kodyvajjha/zymoscope/firmware/main/display/oled.c

/*
 * SSD1306 128x64 OLED I2C driver with built-in 8x8 font
 *
 * Assumes the I2C master driver is already installed (by bme280_init).
 * Shares I2C port 0 with the BME280.
 */

#include "oled.h"

#include <math.h>
#include <string.h>
#include <stdio.h>
#include "driver/i2c.h"
#include "esp_log.h"
#include "sensor/bme280_i2c.h"   /* for BME280_I2C_PORT */

static const char *TAG = "oled";

/* Framebuffer: 128 x 64 pixels = 128 x 8 pages of 8 vertical bits */
#define FB_SIZE  (OLED_WIDTH * (OLED_HEIGHT / 8))
static uint8_t fb[FB_SIZE];

/* ------------------------------------------------------------------ */
/*  Built-in 8x8 ASCII font (printable range 0x20..0x7E)             */
/* ------------------------------------------------------------------ */
static const uint8_t font8x8[][8] = {
    /* 0x20 ' ' */ {0x00,0x00,0x00,0x00,0x00,0x00,0x00,0x00},
    /* 0x21 '!' */ {0x00,0x00,0x06,0x5F,0x5F,0x06,0x00,0x00},
    /* 0x22 '"' */ {0x00,0x03,0x07,0x00,0x00,0x07,0x03,0x00},
    /* 0x23 '#' */ {0x14,0x7F,0x7F,0x14,0x7F,0x7F,0x14,0x00},
    /* 0x24 '$' */ {0x24,0x2E,0x6B,0x6B,0x3A,0x12,0x00,0x00},
    /* 0x25 '%' */ {0x46,0x66,0x30,0x18,0x0C,0x66,0x62,0x00},
    /* 0x26 '&' */ {0x30,0x7A,0x4F,0x5D,0x37,0x7A,0x48,0x00},
    /* 0x27 '\''*/ {0x00,0x04,0x07,0x03,0x00,0x00,0x00,0x00},
    /* 0x28 '(' */ {0x00,0x1C,0x3E,0x63,0x41,0x00,0x00,0x00},
    /* 0x29 ')' */ {0x00,0x41,0x63,0x3E,0x1C,0x00,0x00,0x00},
    /* 0x2A '*' */ {0x08,0x2A,0x3E,0x1C,0x1C,0x3E,0x2A,0x08},
    /* 0x2B '+' */ {0x08,0x08,0x3E,0x3E,0x08,0x08,0x00,0x00},
    /* 0x2C ',' */ {0x00,0x80,0xE0,0x60,0x00,0x00,0x00,0x00},
    /* 0x2D '-' */ {0x08,0x08,0x08,0x08,0x08,0x08,0x00,0x00},
    /* 0x2E '.' */ {0x00,0x00,0x60,0x60,0x00,0x00,0x00,0x00},
    /* 0x2F '/' */ {0x60,0x30,0x18,0x0C,0x06,0x03,0x01,0x00},
    /* 0x30 '0' */ {0x3E,0x7F,0x71,0x59,0x4D,0x7F,0x3E,0x00},
    /* 0x31 '1' */ {0x40,0x42,0x7F,0x7F,0x40,0x40,0x00,0x00},
    /* 0x32 '2' */ {0x62,0x73,0x59,0x49,0x6F,0x66,0x00,0x00},
    /* 0x33 '3' */ {0x22,0x63,0x49,0x49,0x7F,0x36,0x00,0x00},
    /* 0x34 '4' */ {0x18,0x1C,0x16,0x53,0x7F,0x7F,0x50,0x00},
    /* 0x35 '5' */ {0x27,0x67,0x45,0x45,0x7D,0x39,0x00,0x00},
    /* 0x36 '6' */ {0x3C,0x7E,0x4B,0x49,0x79,0x30,0x00,0x00},
    /* 0x37 '7' */ {0x03,0x03,0x71,0x79,0x0F,0x07,0x00,0x00},
    /* 0x38 '8' */ {0x36,0x7F,0x49,0x49,0x7F,0x36,0x00,0x00},
    /* 0x39 '9' */ {0x06,0x4F,0x49,0x69,0x3F,0x1E,0x00,0x00},
    /* 0x3A ':' */ {0x00,0x00,0x36,0x36,0x00,0x00,0x00,0x00},
    /* 0x3B ';' */ {0x00,0x80,0xF6,0x76,0x00,0x00,0x00,0x00},
    /* 0x3C '<' */ {0x08,0x1C,0x36,0x63,0x41,0x00,0x00,0x00},
    /* 0x3D '=' */ {0x24,0x24,0x24,0x24,0x24,0x24,0x00,0x00},
    /* 0x3E '>' */ {0x00,0x41,0x63,0x36,0x1C,0x08,0x00,0x00},
    /* 0x3F '?' */ {0x02,0x03,0x51,0x59,0x0F,0x06,0x00,0x00},
    /* 0x40 '@' */ {0x3E,0x7F,0x41,0x5D,0x5D,0x1F,0x1E,0x00},
    /* 0x41 'A' */ {0x7C,0x7E,0x13,0x13,0x7E,0x7C,0x00,0x00},
    /* 0x42 'B' */ {0x41,0x7F,0x7F,0x49,0x49,0x7F,0x36,0x00},
    /* 0x43 'C' */ {0x1C,0x3E,0x63,0x41,0x41,0x63,0x22,0x00},
    /* 0x44 'D' */ {0x41,0x7F,0x7F,0x41,0x63,0x3E,0x1C,0x00},
    /* 0x45 'E' */ {0x41,0x7F,0x7F,0x49,0x5D,0x41,0x63,0x00},
    /* 0x46 'F' */ {0x41,0x7F,0x7F,0x49,0x1D,0x01,0x03,0x00},
    /* 0x47 'G' */ {0x1C,0x3E,0x63,0x41,0x51,0x73,0x72,0x00},
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
};

/* ------------------------------------------------------------------ */
/*  SSD1306 I2C helpers                                               */
/* ------------------------------------------------------------------ */

static esp_err_t oled_send_cmd(uint8_t cmd)
{
    uint8_t buf[2] = { 0x00, cmd };   /* Co=0, D/C#=0 (command) */
    return i2c_master_write_to_device(BME280_I2C_PORT, OLED_I2C_ADDR,
                                      buf, sizeof(buf),
                                      pdMS_TO_TICKS(100));
}

static esp_err_t oled_send_data(const uint8_t *data, size_t len)
{
    /* Build buffer: control byte (0x40 = Co=0, D/C#=1) + data */
    uint8_t *buf = malloc(len + 1);
    if (!buf) return ESP_ERR_NO_MEM;
    buf[0] = 0x40;
    memcpy(buf + 1, data, len);
    esp_err_t err = i2c_master_write_to_device(BME280_I2C_PORT, OLED_I2C_ADDR,
                                                buf, len + 1,
                                                pdMS_TO_TICKS(200));
    free(buf);
    return err;
}

/** Push the entire framebuffer to the display. */
static void oled_flush(void)
{
    /* Set column address 0..127 */
    oled_send_cmd(0x21); oled_send_cmd(0x00); oled_send_cmd(0x7F);
    /* Set page address 0..7 */
    oled_send_cmd(0x22); oled_send_cmd(0x00); oled_send_cmd(0x07);

    /* Send in 128-byte (one page) chunks to stay within I2C limits */
    for (int page = 0; page < 8; page++) {
        oled_send_data(&fb[page * OLED_WIDTH], OLED_WIDTH);
    }
}

/* ------------------------------------------------------------------ */
/*  Text rendering into the framebuffer                               */
/* ------------------------------------------------------------------ */

/**
 * Draw a character at pixel position (x, page).
 * page is 0..7 (each page = 8 vertical pixels).
 */
static void fb_putchar(int x, int page, char c)
{
    if (c < 0x20 || c > 0x7E) c = '?';
    int idx = c - 0x20;
    int offset = page * OLED_WIDTH + x;
    if (offset + 8 > FB_SIZE) return;
    memcpy(&fb[offset], font8x8[idx], 8);
}

/**
 * Draw a string at (x, page).  Returns the x position after the last
 * character.
 */
static int fb_puts(int x, int page, const char *str)
{
    while (*str && x + 8 <= OLED_WIDTH) {
        fb_putchar(x, page, *str++);
        x += 8;
    }
    return x;
}

/* ------------------------------------------------------------------ */
/*  Public API                                                        */
/* ------------------------------------------------------------------ */

esp_err_t oled_init(void)
{
    /* SSD1306 initialisation sequence for 128x64 */
    static const uint8_t init_cmds[] = {
        0xAE,       /* Display OFF */
        0xD5, 0x80, /* Set display clock div ratio */
        0xA8, 0x3F, /* Set multiplex ratio (64-1) */
        0xD3, 0x00, /* Set display offset = 0 */
        0x40,       /* Set start line = 0 */
        0x8D, 0x14, /* Enable charge pump */
        0x20, 0x00, /* Memory addressing mode = horizontal */
        0xA1,       /* Segment re-map (col 127 = SEG0) */
        0xC8,       /* COM output scan direction (remapped) */
        0xDA, 0x12, /* COM pins hardware config */
        0x81, 0xCF, /* Contrast */
        0xD9, 0xF1, /* Pre-charge period */
        0xDB, 0x40, /* VCOMH deselect level */
        0xA4,       /* Entire display ON (follow RAM) */
        0xA6,       /* Normal display (not inverted) */
        0xAF,       /* Display ON */
    };

    for (size_t i = 0; i < sizeof(init_cmds); i++) {
        esp_err_t err = oled_send_cmd(init_cmds[i]);
        if (err != ESP_OK) {
            ESP_LOGE(TAG, "OLED init cmd 0x%02X failed", init_cmds[i]);
            return err;
        }
    }

    oled_clear();
    ESP_LOGI(TAG, "SSD1306 128x64 OLED initialised (addr=0x%02X)", OLED_I2C_ADDR);
    return ESP_OK;
}

void oled_clear(void)
{
    memset(fb, 0, FB_SIZE);
    oled_flush();
}

void oled_show_status(float temp, float ambient_temp, float setpoint,
                      int heater, int cooler, bool wifi_connected)
{
    memset(fb, 0, FB_SIZE);

    char line[32];

    /* Line 0: Title */
    fb_puts(0, 0, "Zymoscope");

    /* Line 2: Fermentation temperature */
    if (isnan(temp)) {
        fb_puts(0, 2, "Tmp:    -- C");
    } else {
        snprintf(line, sizeof(line), "Tmp: %5.1f C", temp);
        fb_puts(0, 2, line);
    }

    /* Line 3: Ambient temperature */
    snprintf(line, sizeof(line), "Amb: %5.1f C", ambient_temp);
    fb_puts(0, 3, line);

    /* Line 4: Target setpoint */
    snprintf(line, sizeof(line), "Tgt: %5.1f C", setpoint);
    fb_puts(0, 4, line);

    /* Line 5: Plug states */
    snprintf(line, sizeof(line), "Heat:%-3s Cool:%s",
             heater ? "ON" : "OFF", cooler ? "ON" : "OFF");
    fb_puts(0, 5, line);

    /* Line 7: Wi-Fi status */
    fb_puts(0, 7, wifi_connected ? "WiFi: OK" : "WiFi: --");

    oled_flush();
}
